rebekalv/keyboard/images/firmware/usart0initializer.png

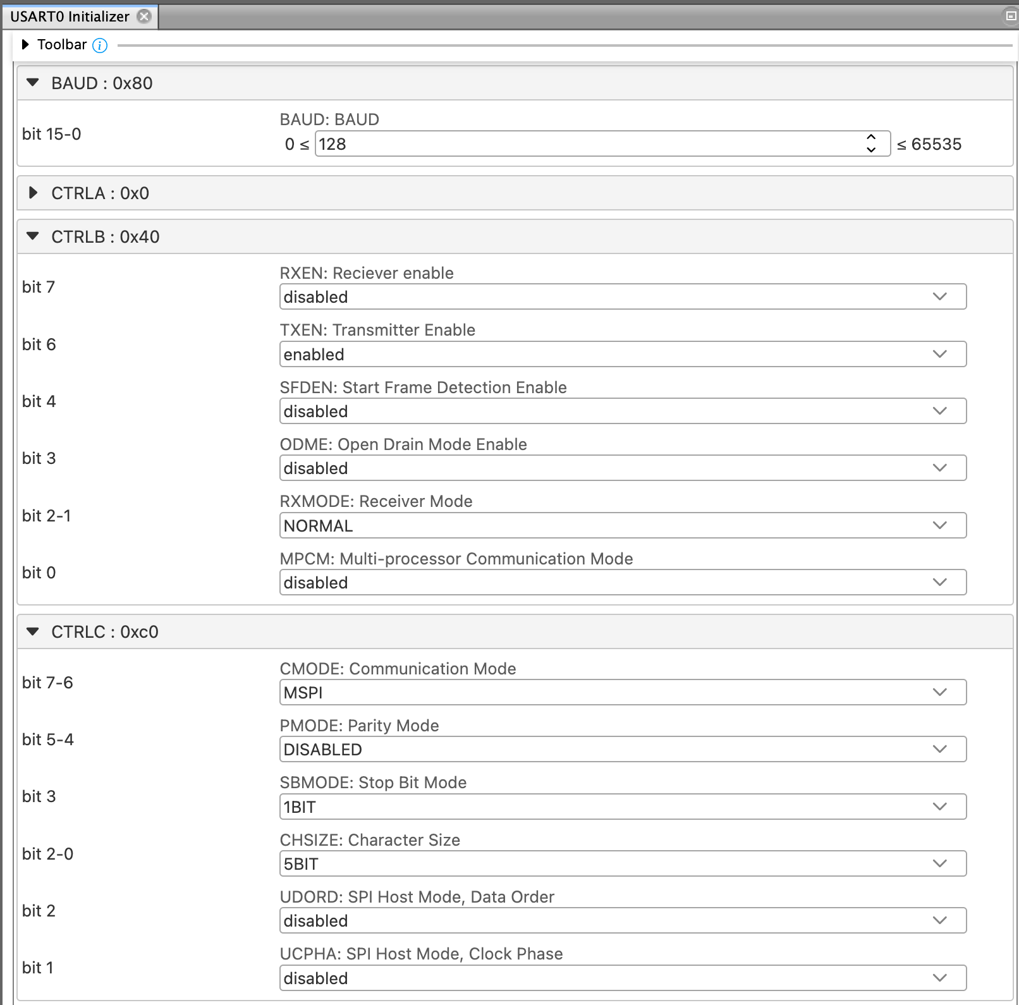
images/firmware/usart0initializer.png
