rebekalv/keyboard/full_keyboard_avrdu.X/usb.c

/*
 * File:   usb.c
 * Author: M70309
 *
 * Created on 26. november 2024, 15:28
 */

#include "usb.h"

#define CONSECUTIVE_EQUAL_PIT_INTERRUPTS 5

RETURN_CODE_t status = SUCCESS;

// USB connection variables
volatile uint8_t vbusFlag = false;

void HandleUSBConnection(void) {
    static volatile uint8_t prevVbusState = 0;

    // Check if VBUS was true last check, indicating that USB was connected
    if (prevVbusState == true)
    {
        // Handle USB Transfers
        status = USBDevice_Handle();
    }
    // Get current status of VBUS
    uint8_t currentVbusState = vbusFlag;
    // If changes to USB VBUS state
    if (currentVbusState != prevVbusState)
    {
        // If USB has been connected
        if (currentVbusState == true)
        {
            // Start USB operations
            status = USB_Start();
        }
        else
        {
            //Stop USB operations
            status = USB_Stop();
        }
        //Save state
        prevVbusState = currentVbusState;
    }
    // If USB error detected, blink LED indicating fault
    if (SUCCESS != status)
    {
        //LED0_Toggle();
    }
}
void CheckUSBConnection(void) {
    // Helper variables for PIT and AC
    static volatile uint8_t PIT_Counter = 0;
    static volatile uint8_t AC_prevState = 0;

    uint8_t AC_currentState = AC0_Read(); // Saves the current state of the AC status register ('1' means above threshold)

    // Makes sure that the AC state has been the same for a certain number of PIT interrupts
    if (PIT_Counter == CONSECUTIVE_EQUAL_PIT_INTERRUPTS)
    {
        if (AC_currentState) // When CMPSTATE is high, the AC output is high which means the VBUS is above the threshold and the pull-up on data+ should be enabled.
        {
            vbusFlag = true;
        }
        else
        {
            vbusFlag = false;
        }
        PIT_Counter++; // Increment the counter to not run start/stop multiple times without an actual state change
    }
    // Increments a counter if the AC has been in the same state for a certain number of PIT interrupts
    else if (AC_currentState == AC_prevState)
    {
        if (PIT_Counter <= CONSECUTIVE_EQUAL_PIT_INTERRUPTS + 1)
        {
            PIT_Counter++;
        }
        else
        {
            ; // Stops counting if the AC has been in the same state for a while.
        }
    }
    else
    {
        PIT_Counter = 0; // Resets the PIT counter if a state change has occurred.
    }
    AC_prevState = AC_currentState;
}
